DevOpsOfChaos/ESP32-SMART-HOME/hardware/shared/esp32-c3-supermini/README.md

# ESP32-C3 SuperMini THT Adapter - KiCad files

> Through-hole adapter board for the TENSTAR ESP32-C3 SuperMini Plus V2.0

## Files

| File | Description |
|---|---|
| `ESP32-C3_SUPERMINI_TH.kicad_sym` | KiCad schematic symbol |
| `MODULE_ESP32-C3_SUPERMINI_TH.kicad_mod` | KiCad footprint (THT) |
| `ESP32-C3_SUPERMINI_TH.step` | 3D model |
| `how-to-import.htm` | import instructions |
