DevOpsOfChaos/ESP32-SMART-HOME/docs/firmware/devices/README.md

# Devices - overview

| Device | File | Short description |
|---|---|---|
| NET-ERL-001 | [NET-ERL-001_hall_module.md](NET-ERL-001_hall_module.md) | hall module (PIR, BME280, VEML7700, 1 relay) |
| NET-ERL-002 | [NET-ERL-002_hall_module_led_ring.md](NET-ERL-002_hall_module_led_ring.md) | extended hall module (LD2410 radar, BME680, ENS160, NeoPixel ring, 1 relay) |
| NET-ZRL-002 | [NET-ZRL-002_shutter_module.md](NET-ZRL-002_shutter_module.md) | shutter module (2 relays, 3 buttons, calibration, position estimate) |
| NET-SEN-002 | [NET-SEN-002_weather_station.md](NET-SEN-002_weather_station.md) | weather sensor (BME280, VEML7700, digital rain input) |
| bat_sen_01 | [bat_sen_01_window_contact.md](bat_sen_01_window_contact.md) | battery window contact (reed, 2x AAA, GPIO wake) |
| bat_sen_02 | [bat_sen_02_rain_sensor.md](bat_sen_02_rain_sensor.md) | battery rain sensor (ADC, hysteresis, timer wake) |
