DevOpsOfChaos/ESP32-SMART-HOME/docs/archive/README.md

# Archive

This folder contains the legacy German reference material that was moved out of the main public documentation path.

## Contents

- `german-reference/public/` - original public technical notes
- `german-reference/ausarbeitung/` - thesis and evidence material
- `german-reference/net_erl_020_bug_report.md` - older device-specific bug note

## Purpose

Keep this material for historical reference only. New readers should start with the English landing pages in the repository root and `docs/`.
