DevOpsOfChaos/ESP32-SMART-HOME/docs/archive/german-reference/public/README.md

# Legacy Reference Notes

This folder keeps the original German technical notes from the project history.

It is reference material, not the main entry point for the public release.

Start with the English files in the repository root and `docs/` if you want the cleaned overview.
