DevOpsOfChaos/ESP32-SMART-HOME/hardware/3d_models/bat_sen/pictures/_frames/gif1/f0079.png

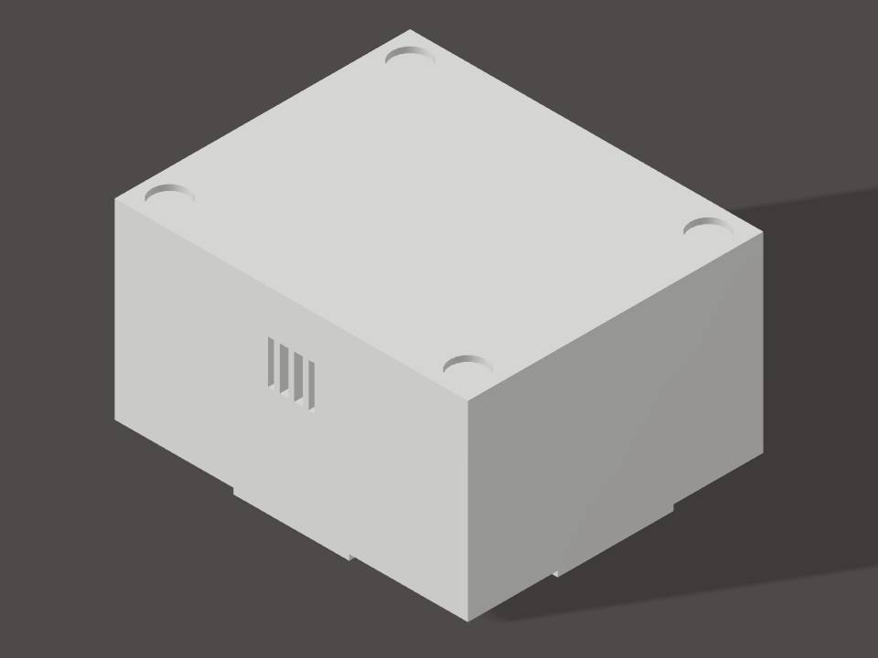
hardware/3d_models/bat_sen/pictures/_frames/gif1/f0079.png
