DevOpsOfChaos/ESP32-SMART-HOME/hardware/3d_models/bat_sen/pictures/_frames/gif2/f0047.png

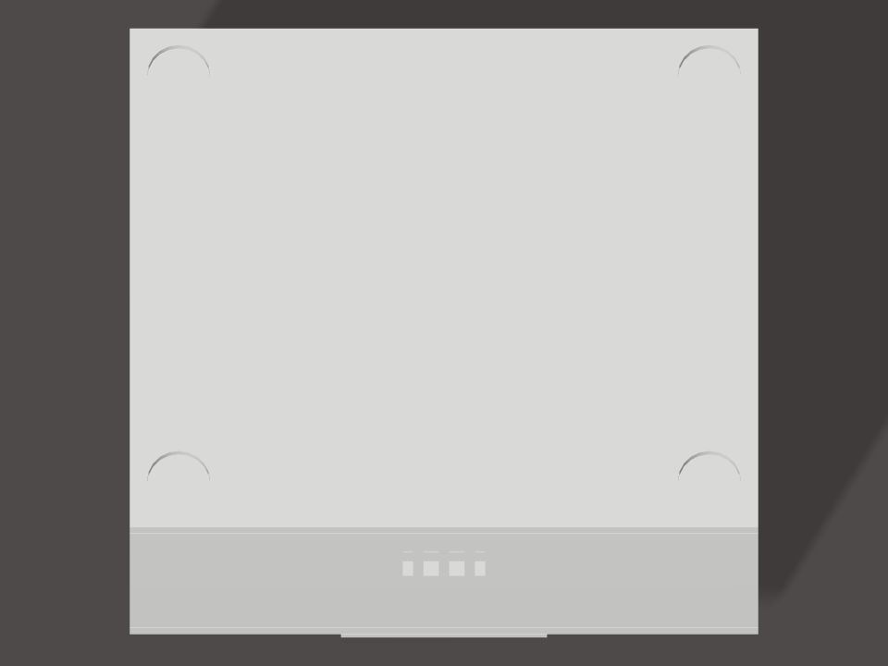
hardware/3d_models/bat_sen/pictures/_frames/gif2/f0047.png
