DevOpsOfChaos/ESP32-SMART-HOME/hardware/3d_models/bat_sen/pictures/_frames/gif3/f0017.png

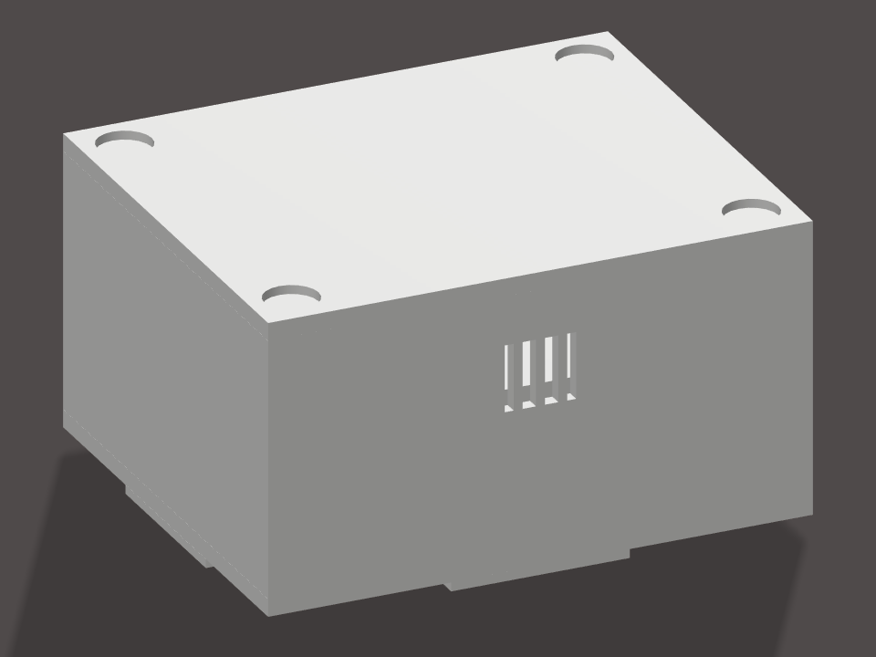
hardware/3d_models/bat_sen/pictures/_frames/gif3/f0017.png
