DevOpsOfChaos/ESP32-SMART-HOME/hardware/3d_models/net_erl/pictures/with_led_ring/deckenlampe_explosion (2).gif

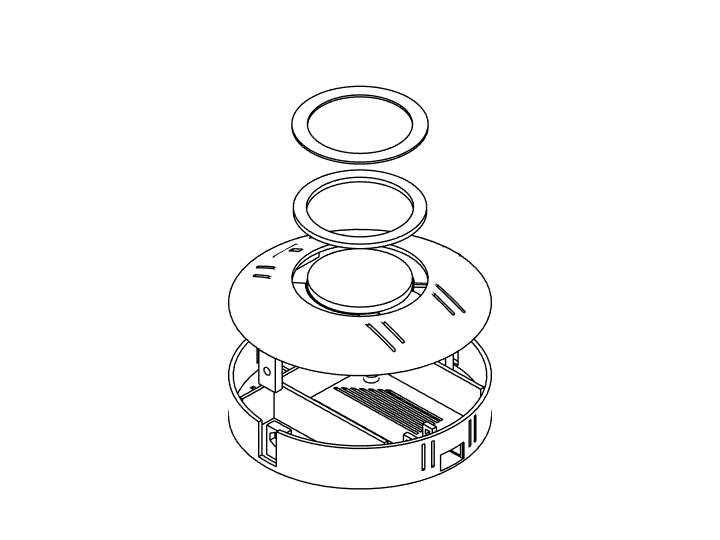
hardware/3d_models/net_erl/pictures/with_led_ring/deckenlampe_explosion (2).gif
