DevOpsOfChaos/ESP32-SMART-HOME/hardware/3d_models/net_erl/pictures/with_led_ring/gif/2/explode_013.png

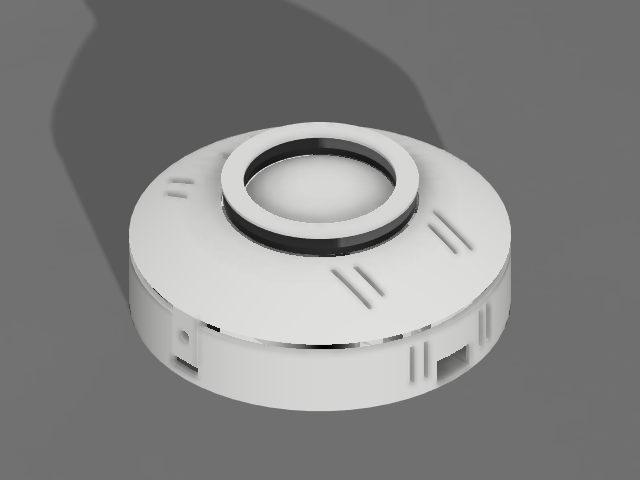
hardware/3d_models/net_erl/pictures/with_led_ring/gif/2/explode_013.png
