DevOpsOfChaos/ESP32-SMART-HOME/hardware/3d_models/net_erl/pictures/with_pir/3/gif1_frame_046.png

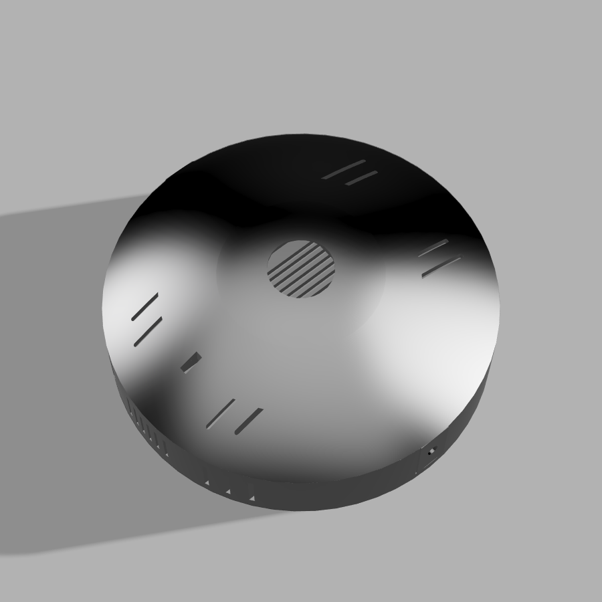
hardware/3d_models/net_erl/pictures/with_pir/3/gif1_frame_046.png
