DevOpsOfChaos/ESP32-SMART-HOME/hardware/3d_models/net_erl/pictures/with_pir/3/gif2_frame_043.png

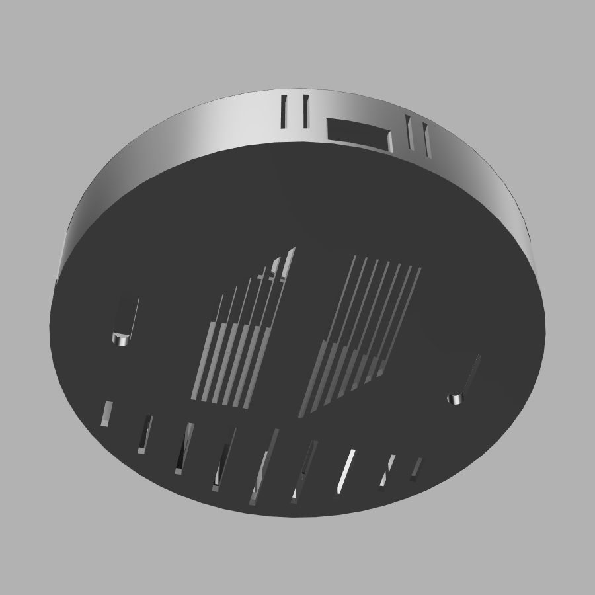
hardware/3d_models/net_erl/pictures/with_pir/3/gif2_frame_043.png
