DevOpsOfChaos/ESP32-SMART-HOME/hardware/3d_models/net_erl/pictures/with_pir/3/gif3_explosion_rotation.gif

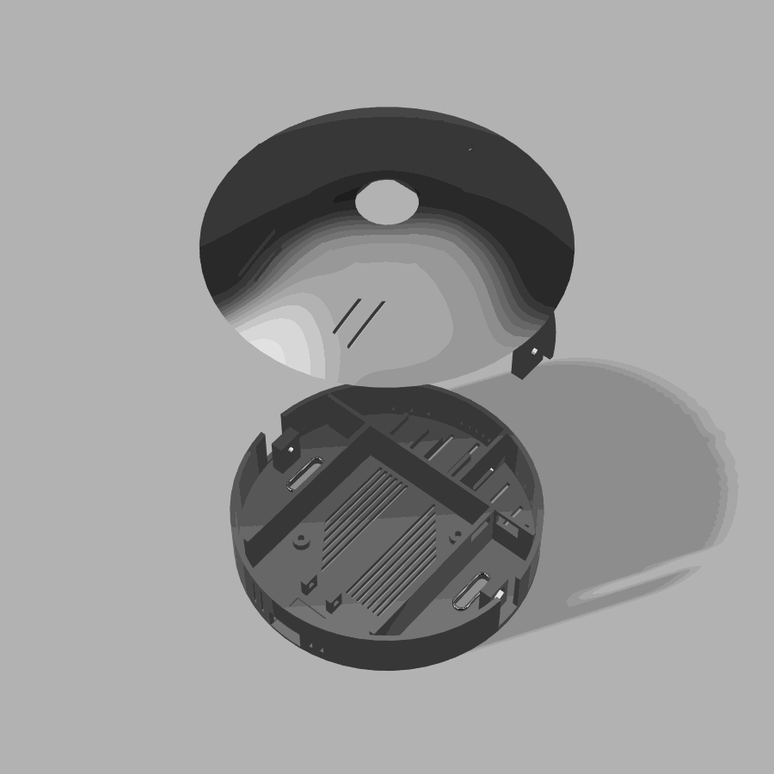
hardware/3d_models/net_erl/pictures/with_pir/3/gif3_explosion_rotation.gif
