DevOpsOfChaos/ESP32-SMART-HOME/hardware/3d_models/net_erl/pictures/with_pir/3/gif3_frame_066.png

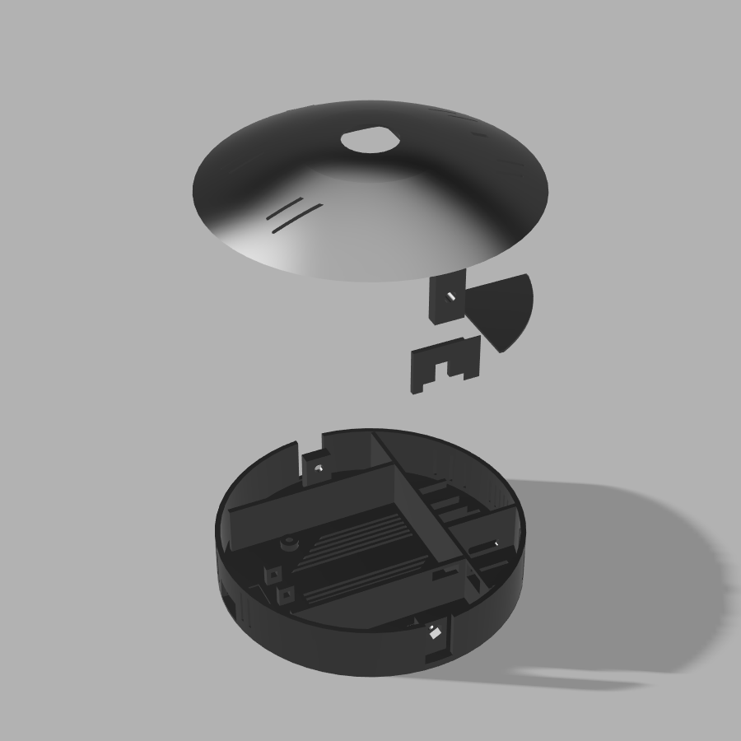
hardware/3d_models/net_erl/pictures/with_pir/3/gif3_frame_066.png
