DevOpsOfChaos/ESP32-SMART-HOME/hardware/3d_models/net_erl/pictures/with_pir/gif1_frame_065.png

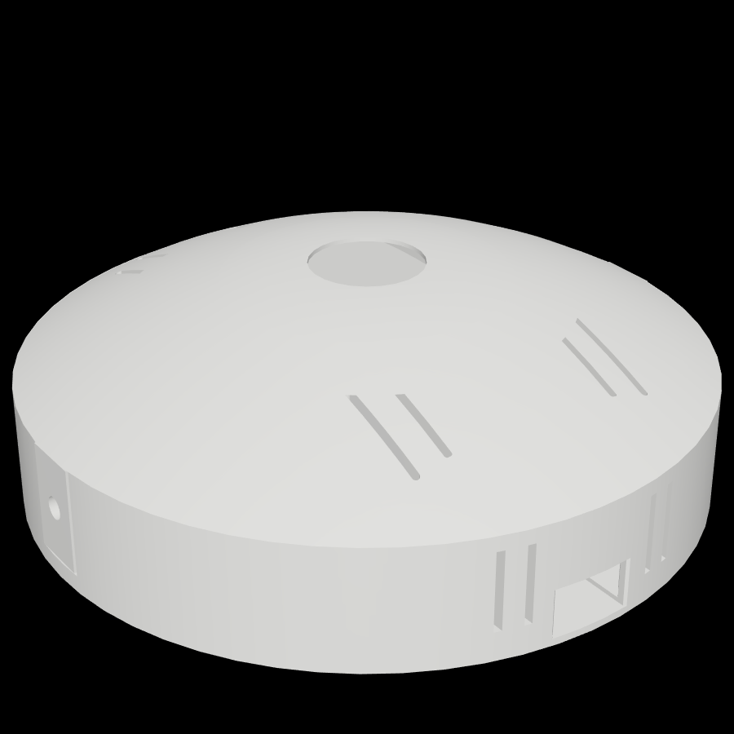
hardware/3d_models/net_erl/pictures/with_pir/gif1_frame_065.png
