DevOpsOfChaos/ESP32-SMART-HOME/hardware/3d_models/net_erl/pictures/with_pir/gif2_frame_025.png

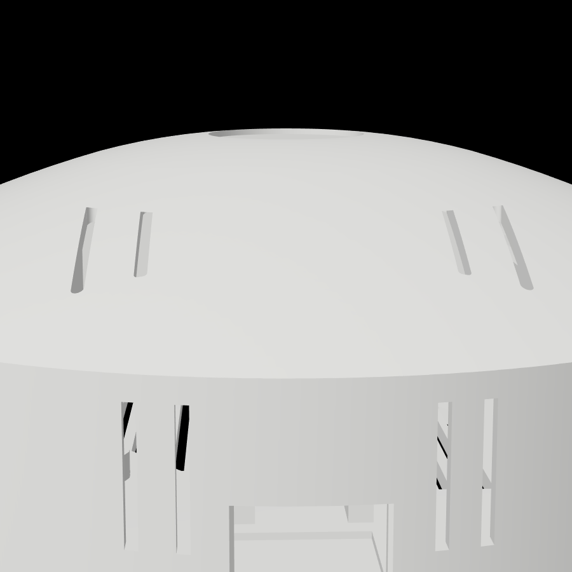
hardware/3d_models/net_erl/pictures/with_pir/gif2_frame_025.png
