DevOpsOfChaos/ESP32-SMART-HOME/hardware/3d_models/net_erl/pictures/with_pir/gif2_top_to_bottom.gif

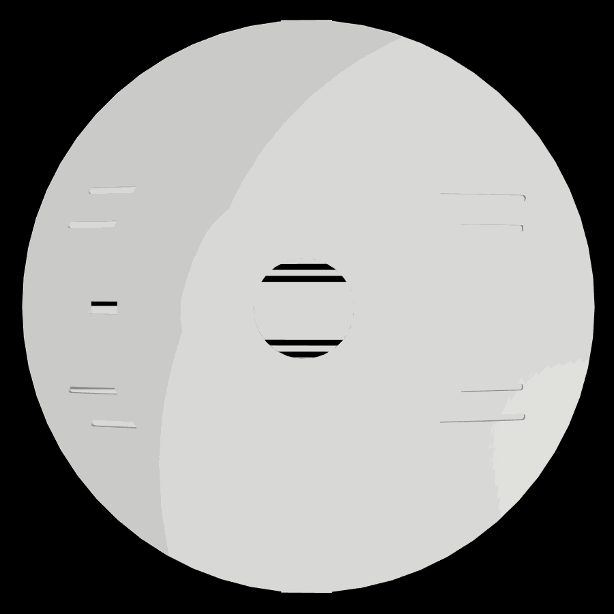
hardware/3d_models/net_erl/pictures/with_pir/gif2_top_to_bottom.gif
