DevOpsOfChaos/ESP32-SMART-HOME/hardware/3d_models/net_erl/pictures/with_pir/gif3_frame_095.png

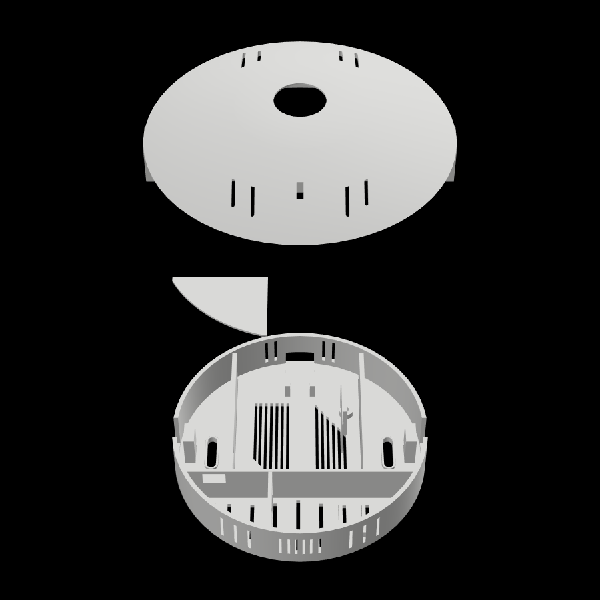
hardware/3d_models/net_erl/pictures/with_pir/gif3_frame_095.png
