DevOpsOfChaos/ESP32-SMART-HOME/hardware/3d_models/net_zrl/pictures/gif_360/frame_020.png

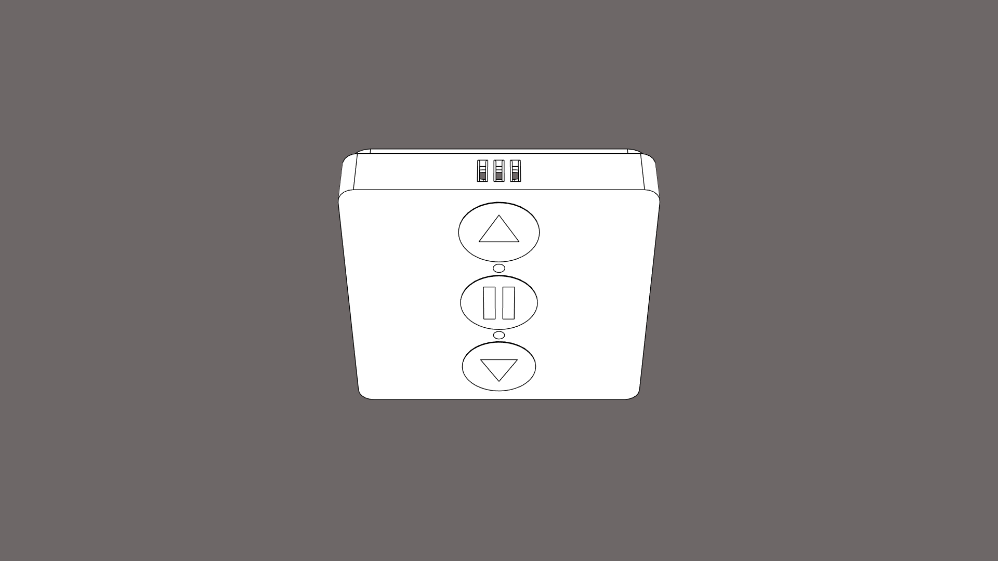
hardware/3d_models/net_zrl/pictures/gif_360/frame_020.png
