DevOpsOfChaos/ESP32-SMART-HOME/hardware/3d_models/net_zrl/pictures/gif_explosion/frame_012.png

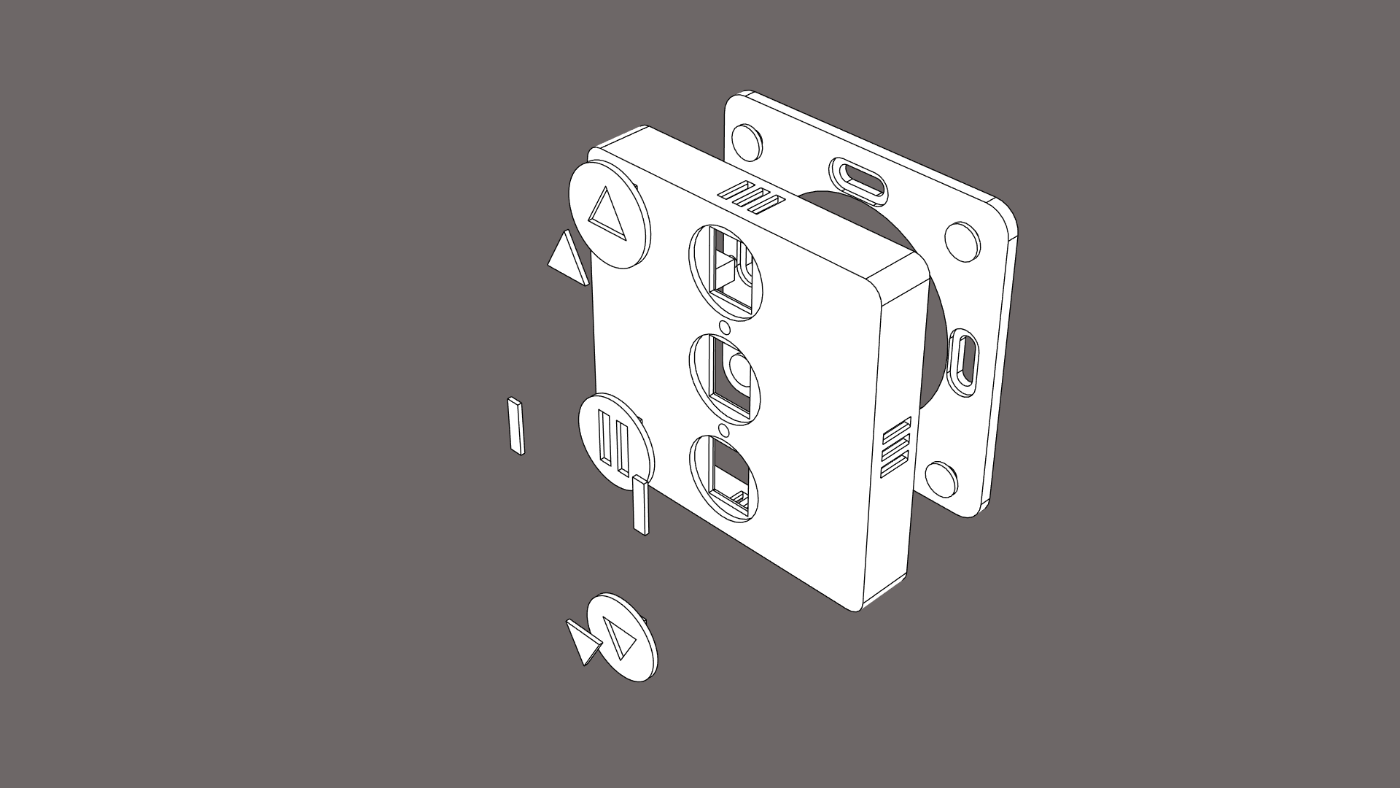
hardware/3d_models/net_zrl/pictures/gif_explosion/frame_012.png
