DevOpsOfChaos/ESP32-SMART-HOME/hardware/3d_models/net_zrl/pictures/gif_product/frame_073.png

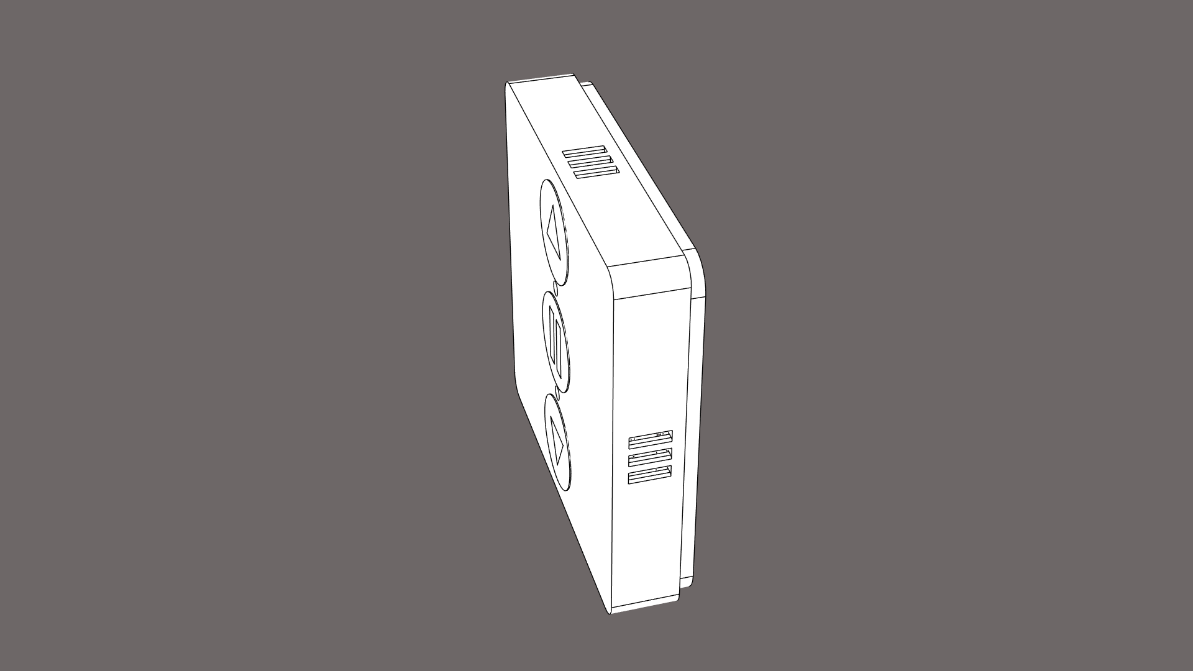
hardware/3d_models/net_zrl/pictures/gif_product/frame_073.png
