DevOpsOfChaos/ESP32-SMART-HOME/hardware/3d_models/net_zrl/zeichen.3mf

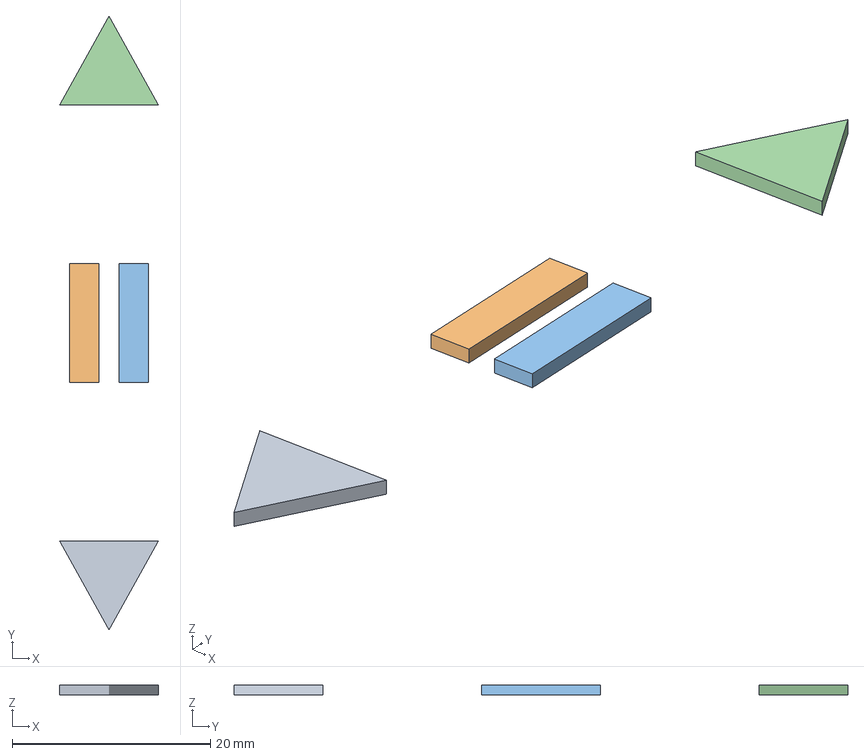
[picture p200: CAD file, 2026-06-07]
hardware/3d_models/net_zrl/zeichen.3mf
10.0 x 62.0 x 1.00 mm
Button_down2
Button_middle1
Button_middle2
Button_up2
