DevOpsOfChaos/ESP32-SMART-HOME/hardware/3d_models/net_erl/Trennwand.3mf

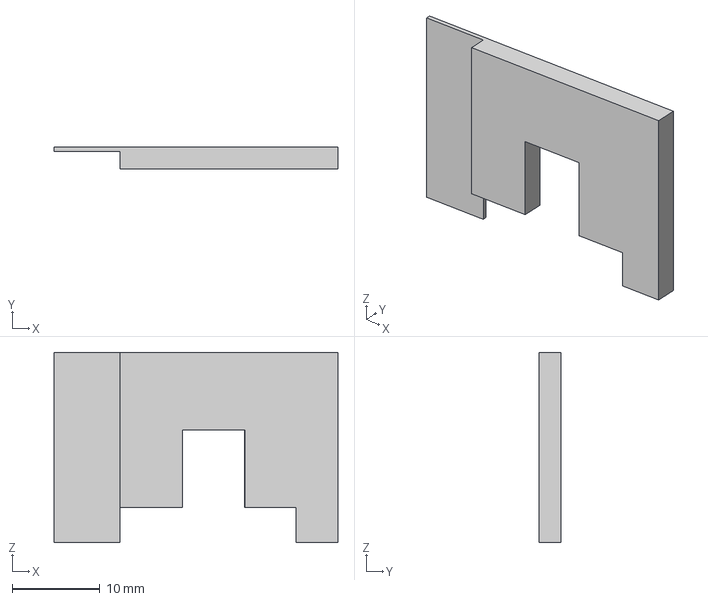
[picture p201: CAD file, 2026-06-07]
hardware/3d_models/net_erl/Trennwand.3mf
32.3 x 2.50 x 21.6 mm
