DevOpsOfChaos/ESP32-SMART-HOME/hardware/3d_models/net_zrl/BODY_FRONT_CONTROL_BASE_V2.3mf

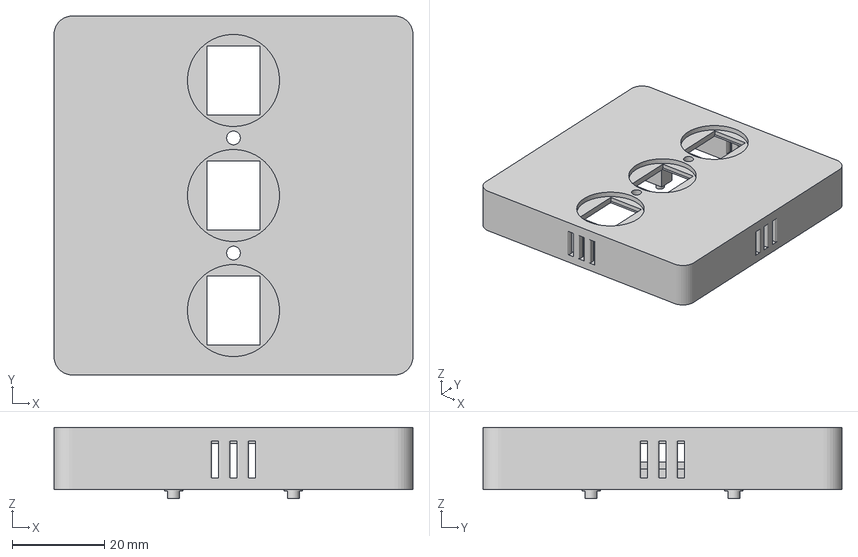
[picture p202: CAD file, 2026-06-07]
hardware/3d_models/net_zrl/BODY_FRONT_CONTROL_BASE_V2.3mf
78.0 x 78.0 x 15.5 mm
