DevOpsOfChaos/ESP32-SMART-HOME/hardware/3d_models/net_erl/Deckel_PIR.3mf

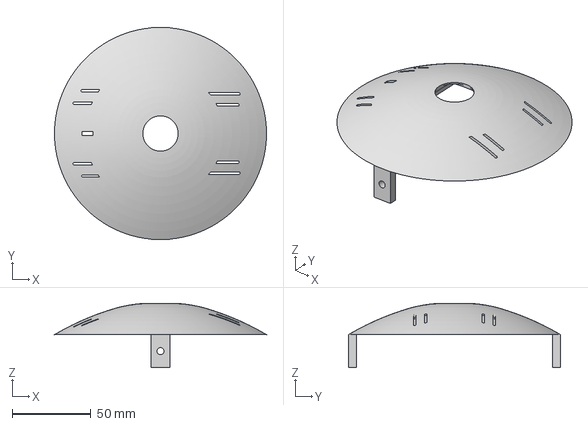
[picture p203: CAD file, 2026-06-07]
hardware/3d_models/net_erl/Deckel_PIR.3mf
134.9 x 135.0 x 40.9 mm
