DevOpsOfChaos/ESP32-SMART-HOME/hardware/3d_models/net_zrl/WALL_ADAPTER_COPY_V2.3mf

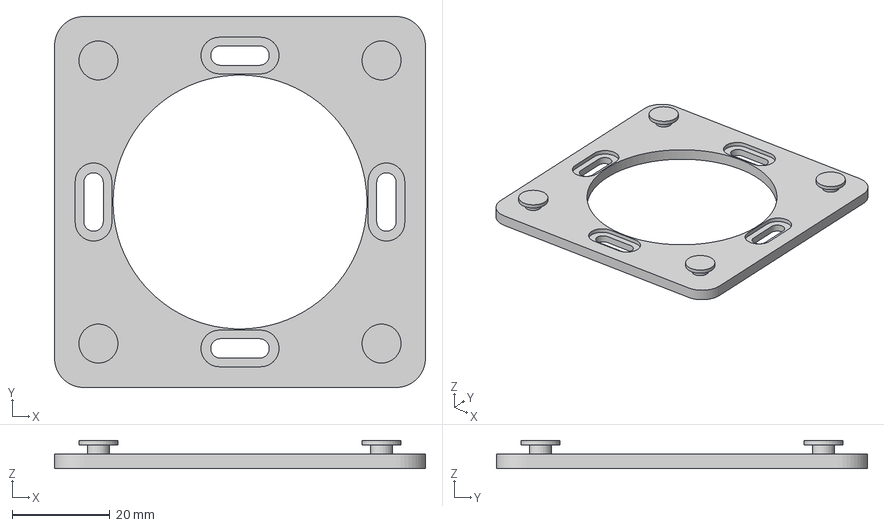
[picture p204: CAD file, 2026-06-07]
hardware/3d_models/net_zrl/WALL_ADAPTER_COPY_V2.3mf
76.0 x 76.0 x 5.80 mm
