DevOpsOfChaos/ESP32-SMART-HOME/hardware/fabrication/schematics/NET-SEN-002-weather-station/Schaltpläne-und-Bilder/NET-SEN-002-weather-station-Sensorik & externe Beschaltung.pdf

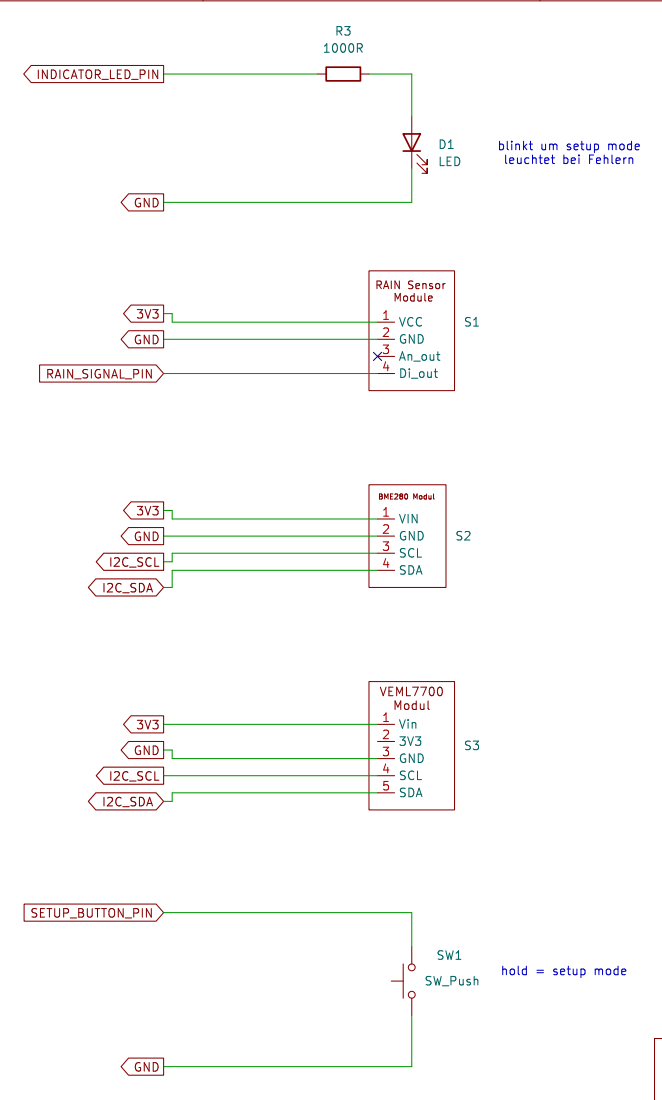
[picture p216: page 1]

blinkt um setup mode

Id: 3/3 Title: Sensorik & externe Beschaltung
