DevOpsOfChaos/ESP32-SMART-HOME/hardware/fabrication/schematics/NET-ZRL-002-shutter-module/Schaltpläne-und-Bilder/NET-ZRL-002-shutter-module-Sensorik & externe Beschaltung.pdf

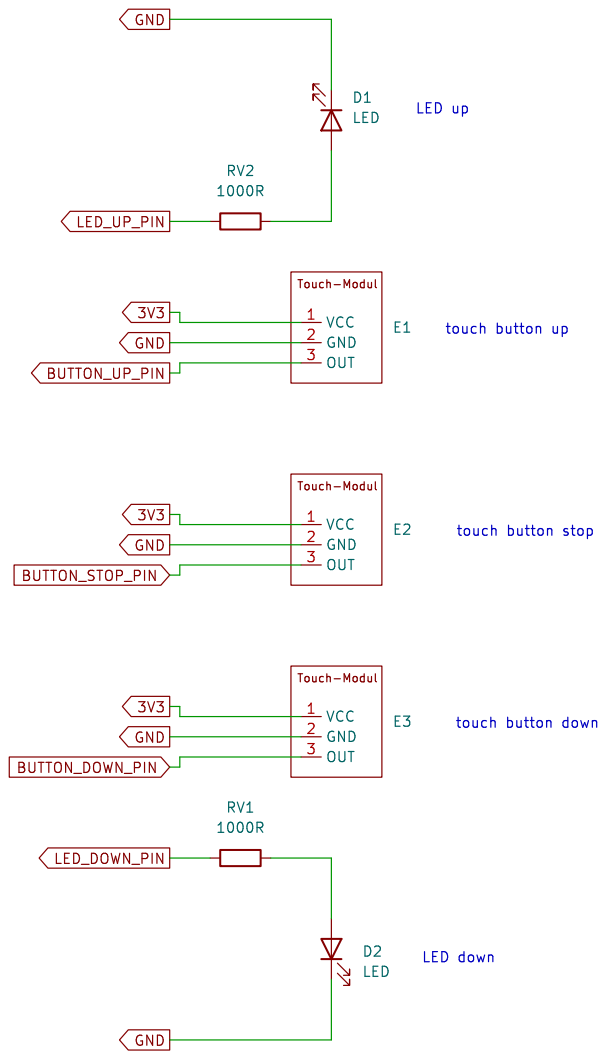
[picture p217: page 1]

Id: 3/3 Title: Sensorik & externe Beschaltung
