DevOpsOfChaos/ESP32-SMART-HOME/hardware/fabrication/schematics/NET-ERL-002-hall-module-led-ring/Schaltpläne-und-Bilder/NET-ERL-002-hall-module-led-ring-Steuerkreis_Controller.pdf

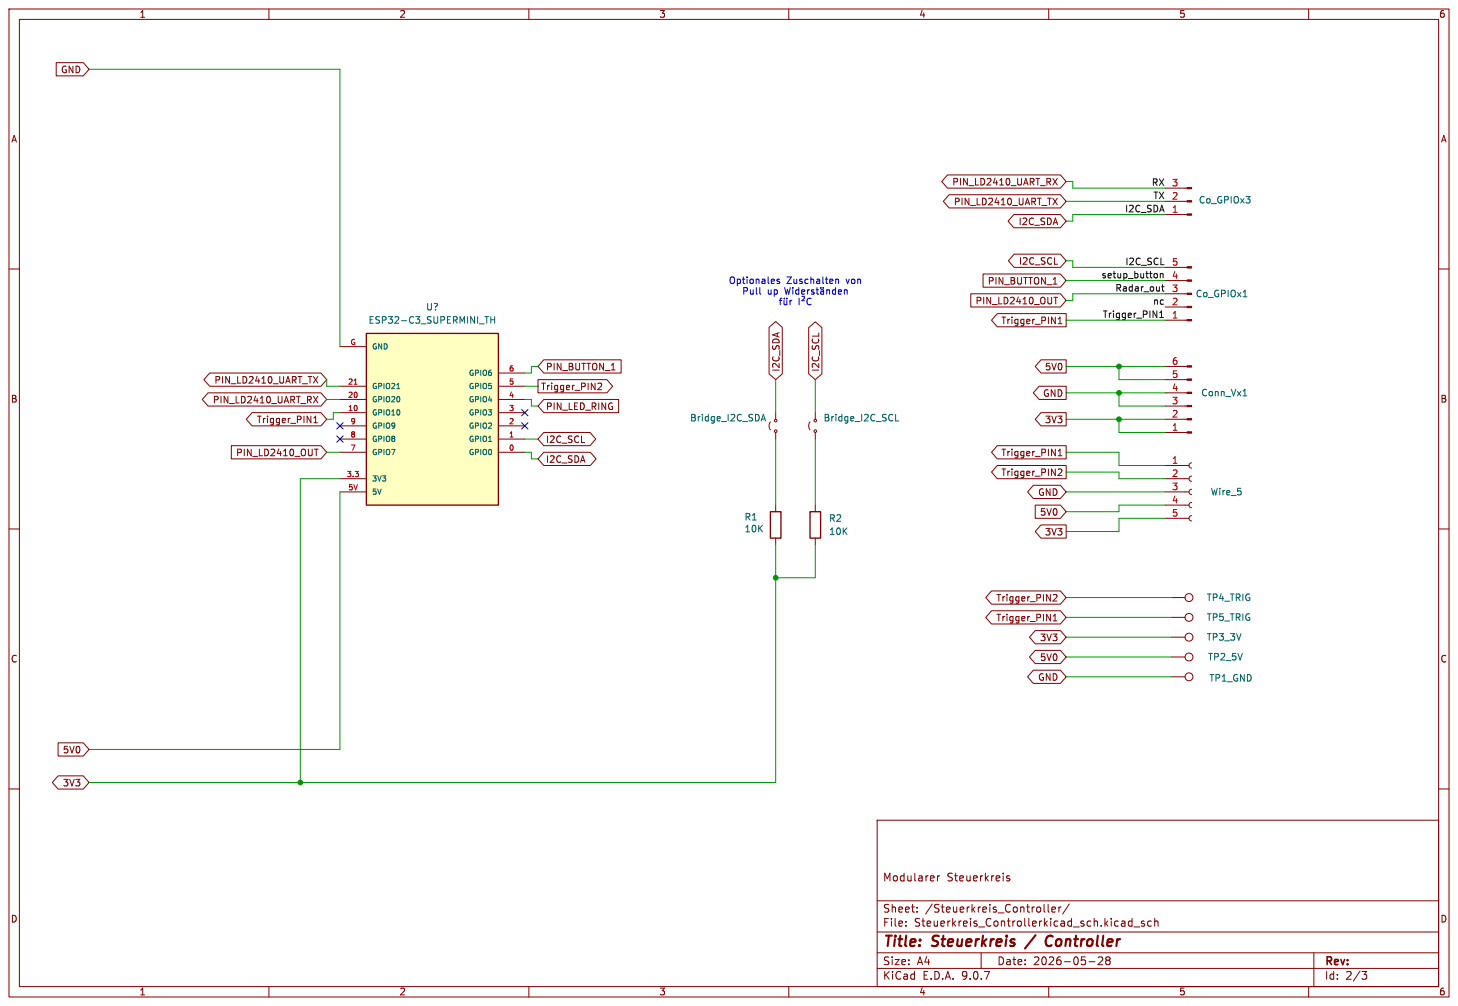
[picture p220: page 1]
