DevOpsOfChaos/ESP32-SMART-HOME/hardware/fabrication/schematics/NET-SEN-002-weather-station/Schaltpläne-und-Bilder/NET-SEN-002-weather-station-Steuerkreis_Controller.pdf

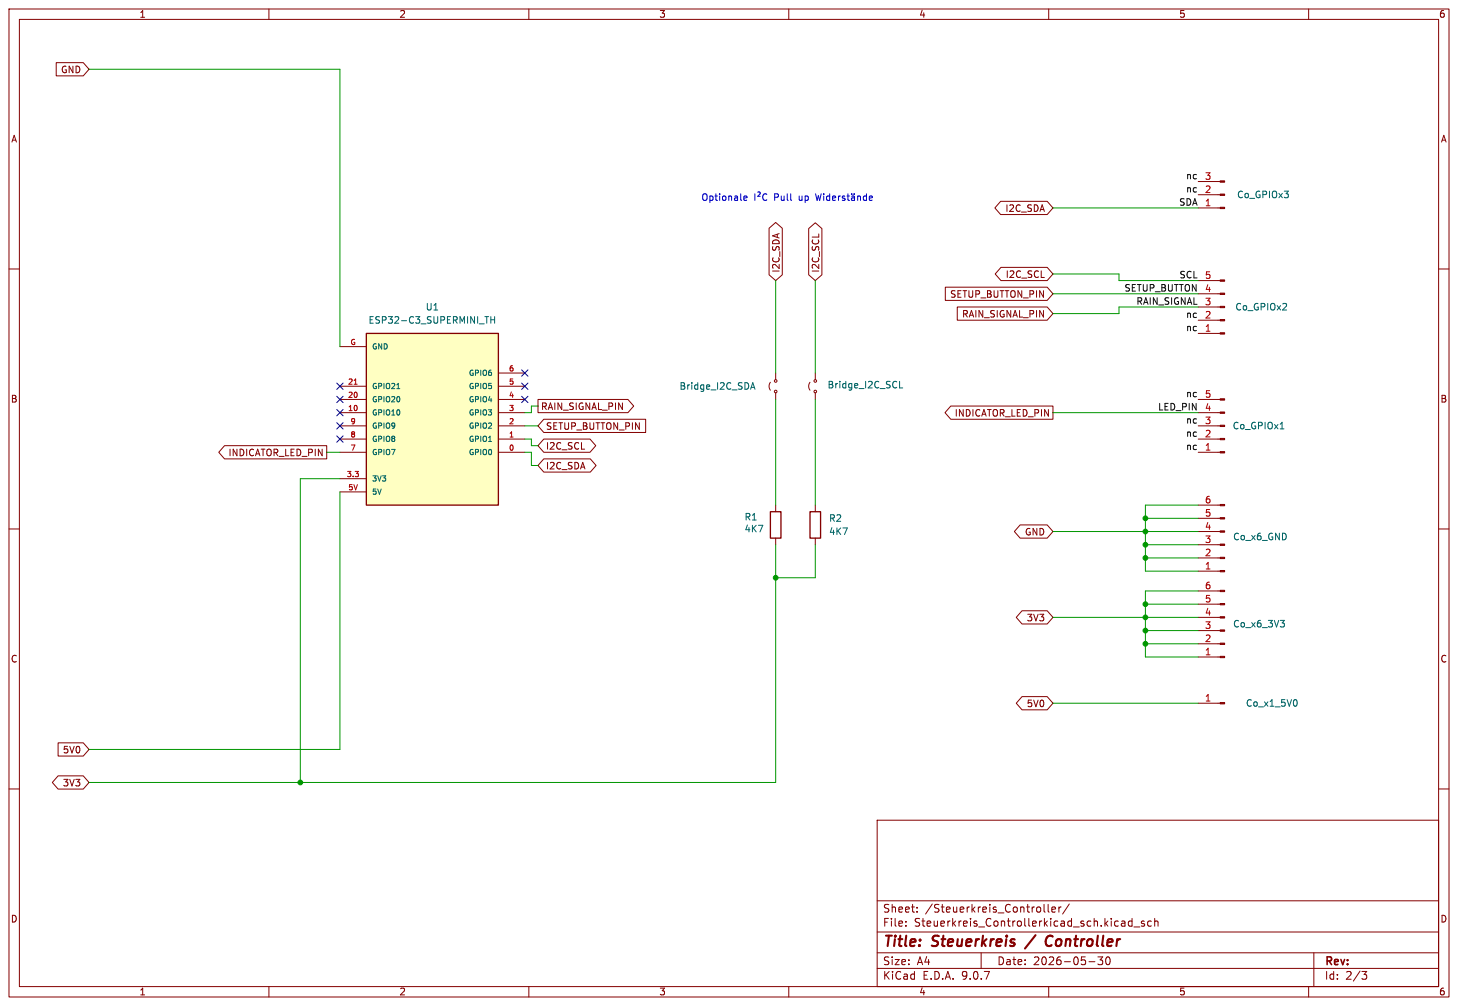
[picture p221: page 1]
