DevOpsOfChaos/ESP32-SMART-HOME/hardware/fabrication/schematics/NET-ZRL-002-shutter-module/Schaltpläne-und-Bilder/NET-ZRL-002-shutter-module-Steuerkreis_Controller.pdf

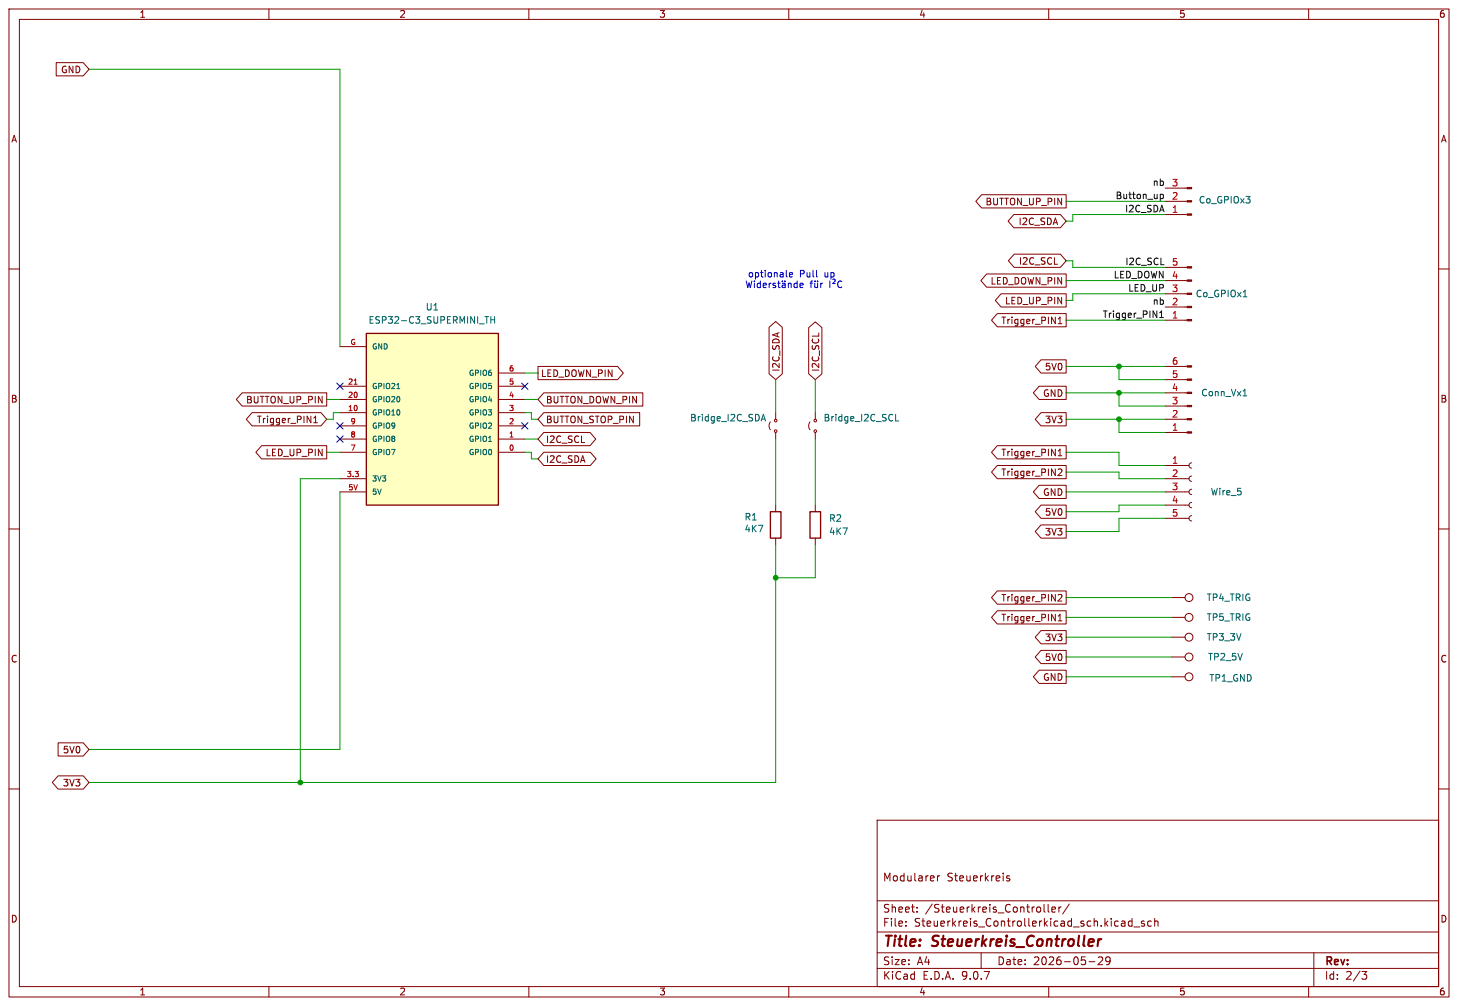
[picture p222: page 1]
